vives-project-xp/TetrisArcadeGame/src/game_console/console/audio.py

from typing import Dict, Optional
import os


class AudioPlayer:
    """Handles audio playback for game sounds."""
    
    def __init__(self, assets_path: str = "assets/sounds/") -> None:
        """
        Initialize audio player.
        
        Args:
            assets_path: Path to sound assets directory
        """
        pass
    
    def load_sound(self, sound_title: str, file_path: str) -> None:
        """
        Load a sound file into memory.
        
        Args:
            sound_title: Identifier for the sound
            file_path: Path to the sound file
        """
        pass
    
    def load_sounds_from_directory(self, directory: str) -> None:
        """
        Load all sound files from a directory.
        
        Args:
            directory: Path to directory containing sound files
        """
        pass
    
    def play_sound(self, sound_title: str, volume: float = 1.0) -> None:
        """
        Play a loaded sound.
        
        Args:
            sound_title: Identifier of the sound to play
            volume: Volume level (0.0 to 1.0)
        """
        pass
    
    def stop_sound(self, sound_title: str) -> None:
        """
        Stop a playing sound.
        
        Args:
            sound_title: Identifier of the sound to stop
        """
        pass
    
    def stop_all(self) -> None:
        """Stop all playing sounds."""
        pass
    
    def set_volume(self, volume: float) -> None:
        """
        Set global volume.
        
        Args:
            volume: Volume level (0.0 to 1.0)
        """
        pass
    
    def cleanup(self) -> None:
        """Clean up audio resources."""
        pass
